Dhruv-x7x/Universal-Wireless-Programmer/others/GUI_flowchart.jpeg

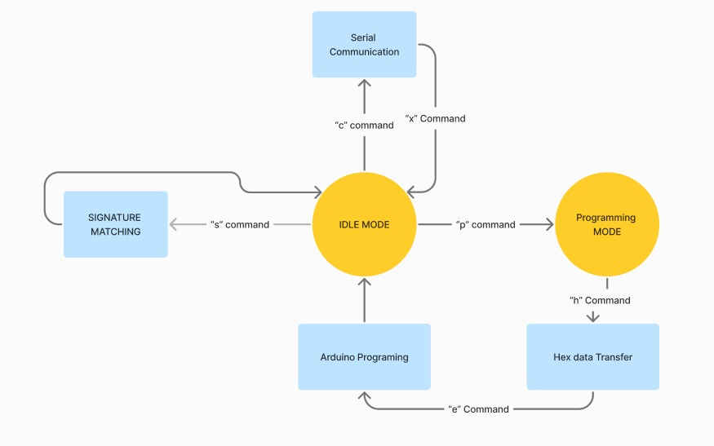
others/GUI_flowchart.jpeg
