Dhruv-x7x/Universal-Wireless-Programmer/pcb/PCB1/pictures/pcb_3d_back.jpeg

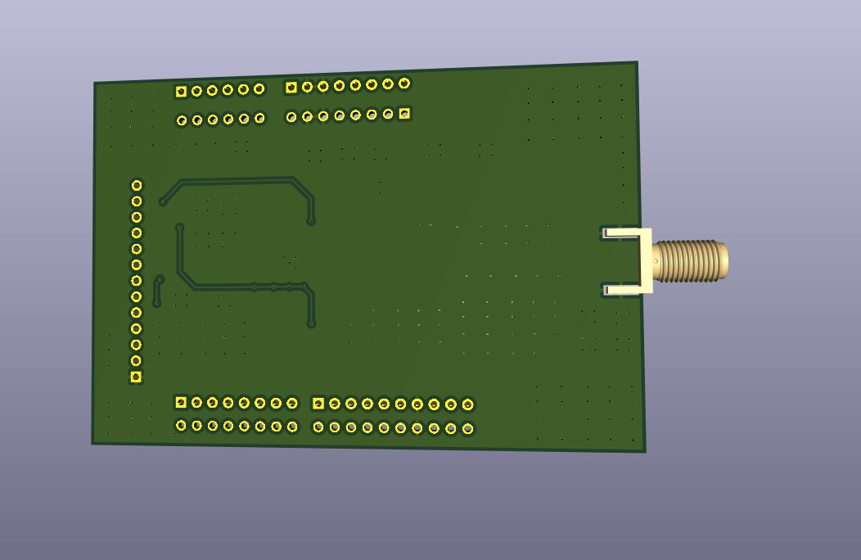
pcb/PCB1/pictures/pcb_3d_back.jpeg
