Dhruv-x7x/Universal-Wireless-Programmer/pcb/PCB1/pictures/pcb_3d_front.jpeg

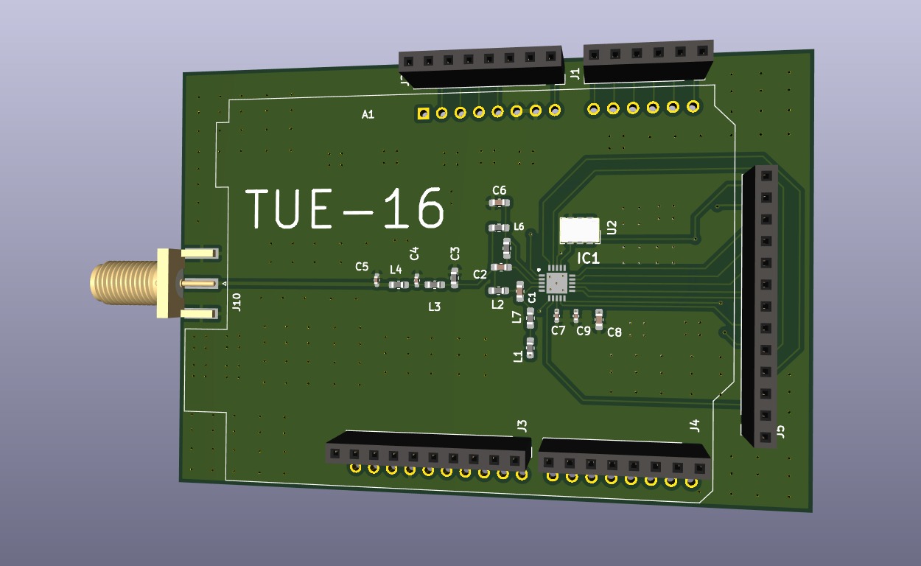
pcb/PCB1/pictures/pcb_3d_front.jpeg
