Dhruv-x7x/Universal-Wireless-Programmer/pcb/PCB1/pictures/pcb_board.jpg

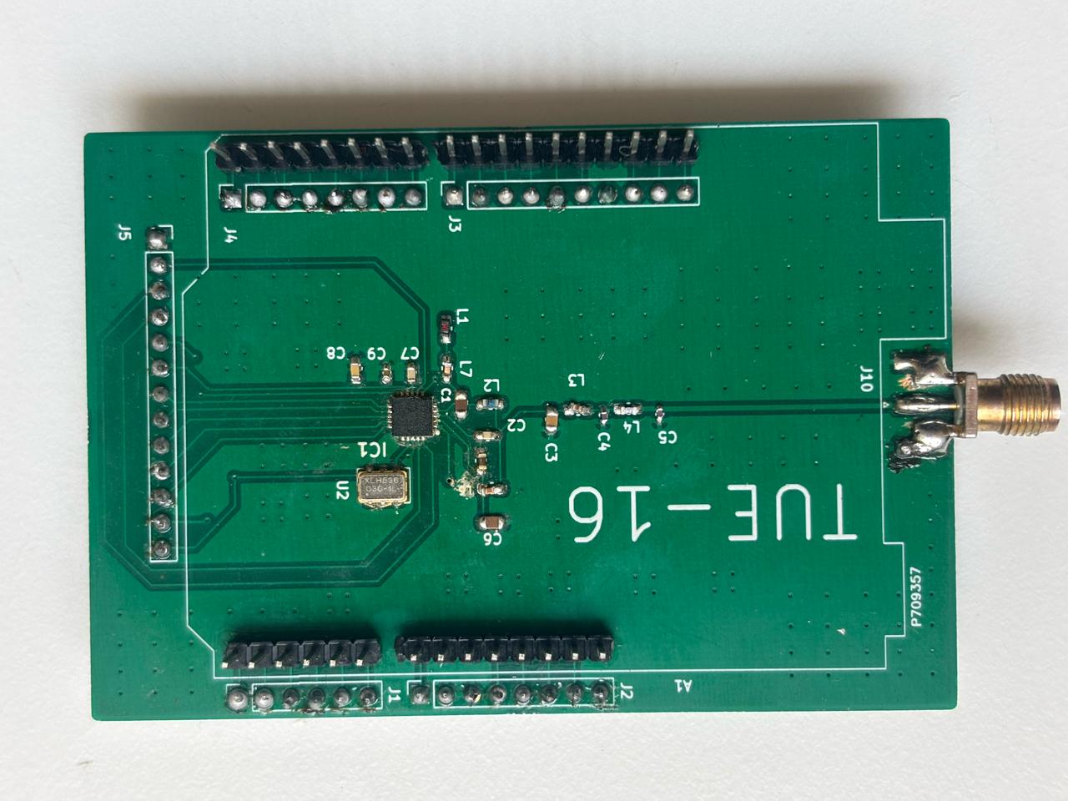
pcb/PCB1/pictures/pcb_board.jpg
