Dhruv-x7x/Universal-Wireless-Programmer/pcb/PCB1/pictures/pcb_with_antenna.jpg

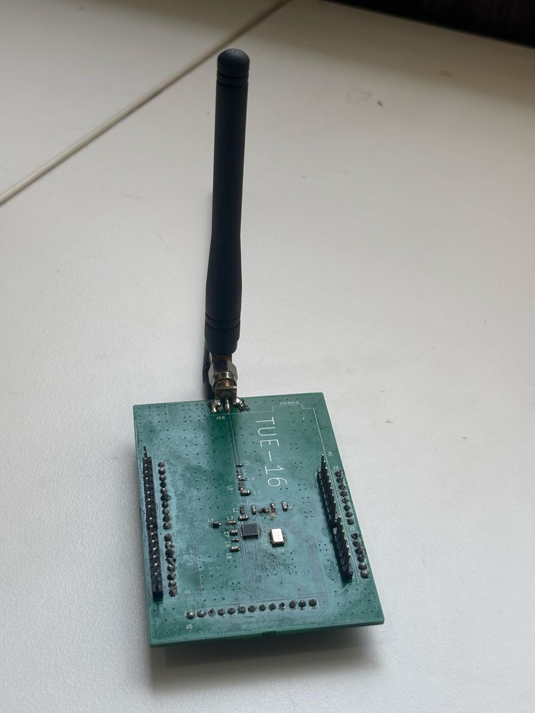
pcb/PCB1/pictures/pcb_with_antenna.jpg
