Dhruv-x7x/Universal-Wireless-Programmer/src/STM32/USB_Detect/Core/Src/main.c

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
/* Includes ------------------------------------------------------------------*/
#include "main.h"
#include "usart.h"
#include "usb_host.h"
#include "gpio.h"
#include <string.h>  /* Include for strcmp */

/* USER CODE BEGIN PD */
#define MAX_BOARD_NAME_LENGTH 50
char detected_board_name[MAX_BOARD_NAME_LENGTH] = "No Device";  // Store the detected board name
char selected_board_name[MAX_BOARD_NAME_LENGTH] = "Arduino UNO R3";  // You can set this to the selected board's name

/* USER CODE END PD */


void SystemClock_Config(void);
void MX_USB_HOST_Process(void);

/**
  * @brief  The application entry point.
  * @retval int
  */
int main(void)
{

  /* MCU Configuration--------------------------------------------------------*/

  /* Reset of all peripherals, Initializes the Flash interface and the Systick. */
  HAL_Init();

  /* Configure the system clock */
  SystemClock_Config();

  /* Initialize all configured peripherals */
  MX_GPIO_Init();
  MX_USART2_UART_Init();
  MX_USB_HOST_Init();
  /* Infinite loop */
  /* USER CODE BEGIN WHILE */
  while (1)
  {
      const char* detected_device = check_usb_device();  // Get the name of the detected device
      strncpy(detected_board_name, detected_device, MAX_BOARD_NAME_LENGTH - 1);
      detected_board_name[MAX_BOARD_NAME_LENGTH - 1] = '\0'; // Ensure null termination

      if (strcmp(detected_board_name, "No Device") == 0) {
          // If no device is detected, do nothing or handle accordingly
          printf("No USB device detected.\r\n");
      } else {
          // If a device is detected, check if it matches the selected board
          if (strcmp(detected_board_name, selected_board_name) == 0) {
              printf("Detected board matches the selected board: %s\r\n", detected_board_name);
              if (strcmp(detected_board_name, "Arduino UNO R3") == 0) {  // Corrected comparison
                      printf("Triggering bootloader\r\n");
                      trigger_arduino_bootloader();
                  }
          } else {
              printf("Board mismatch! Detected: %s, Selected: %s\r\n", detected_board_name, selected_board_name);
          }
      }

      MX_USB_HOST_Process();  // Process USB Host tasks
      HAL_Delay(250);  // Small delay to avoid too fast polling
  }

  /* USER CODE END 3 */
}

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
