Dhruv-x7x/Universal-Wireless-Programmer/src/STM32/HardcodeRXTX/Core/Inc/arduino_hex.h

/**
  * @file    arduino_hex.h
  * @brief   Arduino hex file data
  * @details Contains the hex file data to be programmed to the Arduino
  *          Generated from Blink.ino.hex
  */

#ifndef ARDUINO_HEX_H
#define ARDUINO_HEX_H
#include <stdint.h>


/* Arduino hex file data as byte array */
const uint8_t arduino_hex_data[] = {
    /* Line 1 */
    ':', '1', '0', '0', '0', '0', '0', '0', '0', '0', 'C', '9', '4', '5', 'C', '0',
    '0', '0', 'C', '9', '4', '6', 'E', '0', '0', '0', 'C', '9', '4', '6', 'E', '0',
    '0', '0', 'C', '9', '4', '6', 'E', '0', '0', 'C', 'A',
    /* Line 2 */
    ':', '1', '0', '0', '0', '1', '0', '0', '0', '0', 'C', '9', '4', '6', 'E', '0',
    '0', '0', 'C', '9', '4', '6', 'E', '0', '0', '0', 'C', '9', '4', '6', 'E', '0',
    '0', '0', 'C', '9', '4', '6', 'E', '0', '0', 'A', '8',
    /* Line 3 */
    ':', '1', '0', '0', '0', '2', '0', '0', '0', '0', 'C', '9', '4', '6', 'E', '0',
    '0', '0', 'C', '9', '4', '6', 'E', '0', '0', '0', 'C', '9', '4', '6', 'E', '0',
    '0', '0', 'C', '9', '4', '6', 'E', '0', '0', '9', '8',
    /* Line 4 */
    ':', '1', '0', '0', '0', '3', '0', '0', '0', '0', 'C', '9', '4', '6', 'E', '0',
    '0', '0', 'C', '9', '4', '6', 'E', '0', '0', '0', 'C', '9', '4', '6', 'E', '0',
    '0', '0', 'C', '9', '4', '6', 'E', '0', '0', '8', '8',
    /* Line 5 */
    ':', '1', '0', '0', '0', '4', '0', '0', '0', '0', 'C', '9', '4', '1', '3', '0',
    '1', '0', 'C', '9', '4', '6', 'E', '0', '0', '0', 'C', '9', '4', '6', 'E', '0',
    '0', '0', 'C', '9', '4', '6', 'E', '0', '0', 'D', '2',
    /* Line 6 */
    ':', '1', '0', '0', '0', '5', '0', '0', '0', '0', 'C', '9', '4', '6', 'E', '0',
    '0', '0', 'C', '9', '4', '6', 'E', '0', '0', '0', 'C', '9', '4', '6', 'E', '0',
    '0', '0', 'C', '9', '4', '6', 'E', '0', '0', '6', '8',
    /* Line 7 */
    ':', '1', '0', '0', '0', '6', '0', '0', '0', '0', 'C', '9', '4', '6', 'E', '0',
    '0', '0', 'C', '9', '4', '6', 'E', '0', '0', '0', '0', '0', '0', '0', '0', '0',
    '0', '2', '4', '0', '0', '2', '7', '0', '0', '2', '9',
    /* Line 8 */
    ':', '1', '0', '0', '0', '7', '0', '0', '0', '2', 'A', '0', '0', '0', '0', '0',
    '0', '0', '0', '0', '0', '2', '5', '0', '0', '2', '8', '0', '0', '2', 'B', '0',
    '0', '0', '4', '0', '4', '0', '4', '0', '4', 'C', 'E',
    /* Line 9 */
    ':', '1', '0', '0', '0', '8', '0', '0', '0', '0', '4', '0', '4', '0', '4', '0',
    '4', '0', '2', '0', '2', '0', '2', '0', '2', '0', '2', '0', '2', '0', '3', '0',
    '3', '0', '3', '0', '3', '0', '3', '0', '3', '4', '2',
    /* Line 10 */
    ':', '1', '0', '0', '0', '9', '0', '0', '0', '0', '1', '0', '2', '0', '4', '0',
    '8', '1', '0', '2', '0', '4', '0', '8', '0', '0', '1', '0', '2', '0', '4', '0',
    '8', '1', '0', '2', '0', '0', '1', '0', '2', '1', 'F',
    /* Line 11 */
    ':', '1', '0', '0', '0', 'A', '0', '0', '0', '0', '4', '0', '8', '1', '0', '2',
    '0', '0', '0', '0', '0', '0', '0', '0', '8', '0', '0', '0', '2', '0', '1', '0',
    '0', '0', '0', '0', '3', '0', '4', '0', '7', 'F', 'B',
    /* Line 12 */
    ':', '1', '0', '0', '0', 'B', '0', '0', '0', '0', '0', '0', '0', '0', '0', '0',
    '0', '0', '0', '0', '0', '0', '0', '0', '0', '1', '1', '2', '4', '1', 'F', 'B',
    'E', 'C', 'F', 'E', 'F', 'D', '8', 'E', '0', 'B', '8',
    /* Line 13 */
    ':', '1', '0', '0', '0', 'C', '0', '0', '0', 'D', 'E', 'B', 'F', 'C', 'D', 'B',
    'F', '2', '1', 'E', '0', 'A', '0', 'E', '0', 'B', '1', 'E', '0', '0', '1', 'C',
    '0', '1', 'D', '9', '2', 'A', '9', '3', '0', 'A', 'C',
    /* Line 14 */
    ':', '1', '0', '0', '0', 'D', '0', '0', '0', 'B', '2', '0', '7', 'E', '1', 'F',
    '7', '0', 'E', '9', '4', '5', 'D', '0', '1', '0', 'C', '9', '4', 'C', 'C', '0',
    '1', '0', 'C', '9', '4', '0', '0', '0', '0', '8', '2',
    /* Line 15 */
    ':', '1', '0', '0', '0', 'E', '0', '0', '0', 'E', '1', 'E', 'B', 'F', '0', 'E',
    '0', '2', '4', '9', '1', 'E', 'D', 'E', '9', 'F', '0', 'E', '0', '9', '4', '9',
    '1', 'E', '9', 'E', '8', 'F', '0', 'E', '0', '5', '3',
    /* Line 16 */
    ':', '1', '0', '0', '0', 'F', '0', '0', '0', 'E', '4', '9', '1', 'E', 'E', '2',
    '3', 'C', '9', 'F', '0', '2', '2', '2', '3', '3', '9', 'F', '0', '2', '3', '3',
    '0', '0', '1', 'F', '1', 'A', '8', 'F', '4', '7', '2',
    /* Line 17 */
    ':', '1', '0', '0', '1', '0', '0', '0', '0', '2', '1', '3', '0', '1', '9', 'F',
    '1', '2', '2', '3', '0', '2', '9', 'F', '1', 'F', '0', 'E', '0', 'E', 'E', '0',
    'F', 'F', 'F', '1', 'F', 'E', 'E', '5', '8', 'F', '7',
    /* Line 18 */
    ':', '1', '0', '0', '1', '1', '0', '0', '0', 'F', 'F', '4', 'F', 'A', '5', '9',
    '1', 'B', '4', '9', '1', '2', 'F', 'B', '7', 'F', '8', '9', '4', 'E', 'C', '9',
    '1', '8', '1', '1', '1', '2', '6', 'C', '0', 'A', 'F',
    /* Line 19 */
    ':', '1', '0', '0', '1', '2', '0', '0', '0', '9', '0', '9', '5', '9', 'E', '2',
    '3', '9', 'C', '9', '3', '2', 'F', 'B', 'F', '0', '8', '9', '5', '2', '7', '3',
    '0', 'A', '9', 'F', '0', '2', '8', '3', '0', 'E', '7',
    /* Line 20 */
    ':', '1', '0', '0', '1', '3', '0', '0', '0', 'C', '9', 'F', '0', '2', '4', '3',
    '0', '4', '9', 'F', '7', '2', '0', '9', '1', '8', '0', '0', '0', '2', 'F', '7',
    'D', '0', '3', 'C', '0', '2', '0', '9', '1', '2', '1',
    /* Line 21 */
    ':', '1', '0', '0', '1', '4', '0', '0', '0', '8', '0', '0', '0', '2', 'F', '7',
    '7', '2', '0', '9', '3', '8', '0', '0', '0', 'D', 'F', 'C', 'F', '2', '4', 'B',
    '5', '2', 'F', '7', '7', '2', '4', 'B', 'D', '4', '8',
    /* Line 22 */
    ':', '1', '0', '0', '1', '5', '0', '0', '0', 'D', 'B', 'C', 'F', '2', '4', 'B',
    '5', '2', 'F', '7', 'D', 'F', 'B', 'C', 'F', '2', '0', '9', '1', 'B', '0', '0',
    '0', '2', 'F', '7', '7', '2', '0', '9', '3', 'E', 'C',
    /* Line 23 */
    ':', '1', '0', '0', '1', '6', '0', '0', '0', 'B', '0', '0', '0', 'D', '2', 'C',
    'F', '2', '0', '9', '1', 'B', '0', '0', '0', '2', 'F', '7', 'D', 'F', '9', 'C',
    'F', '9', 'E', '2', 'B', 'D', 'A', 'C', 'F', 'F', '7',
    /* Line 24 */
    ':', '1', '0', '0', '1', '7', '0', '0', '0', '3', 'F', 'B', '7', 'F', '8', '9',
    '4', '8', '0', '9', '1', '0', '5', '0', '1', '9', '0', '9', '1', '0', '6', '0',
    '1', 'A', '0', '9', '1', '0', '7', '0', '1', '8', '5',
    /* Line 25 */
    ':', '1', '0', '0', '1', '8', '0', '0', '0', 'B', '0', '9', '1', '0', '8', '0',
    '1', '2', '6', 'B', '5', 'A', '8', '9', 'B', '0', '5', 'C', '0', '2', 'F', '3',
    'F', '1', '9', 'F', '0', '0', '1', '9', '6', '3', '4',
    /* Line 26 */
    ':', '1', '0', '0', '1', '9', '0', '0', '0', 'A', '1', '1', 'D', 'B', '1', '1',
    'D', '3', 'F', 'B', 'F', 'B', 'A', '2', 'F', 'A', '9', '2', 'F', '9', '8', '2',
    'F', '8', '8', '2', '7', 'B', 'C', '0', '1', 'E', '1',
    /* Line 27 */
    ':', '1', '0', '0', '1', 'A', '0', '0', '0', 'C', 'D', '0', '1', '6', '2', '0',
    'F', '7', '1', '1', 'D', '8', '1', '1', 'D', '9', '1', '1', 'D', '4', '2', 'E',
    '0', '6', '6', '0', 'F', '7', '7', '1', 'F', '0', '9',
    /* Line 28 */
    ':', '1', '0', '0', '1', 'B', '0', '0', '0', '8', '8', '1', 'F', '9', '9', '1',
    'F', '4', 'A', '9', '5', 'D', '1', 'F', '7', '0', '8', '9', '5', '8', 'F', '9',
    '2', '9', 'F', '9', '2', 'A', 'F', '9', '2', '0', '9',
    /* Line 29 */
    ':', '1', '0', '0', '1', 'C', '0', '0', '0', 'B', 'F', '9', '2', 'C', 'F', '9',
    '2', 'D', 'F', '9', '2', 'E', 'F', '9', '2', 'F', 'F', '9', '2', '0', 'E', '9',
    '4', 'B', '8', '0', '0', '4', 'B', '0', '1', '5', '4',
    /* Line 30 */
    ':', '1', '0', '0', '1', 'D', '0', '0', '0', '5', 'C', '0', '1', '8', '8', 'E',
    'E', 'C', '8', '2', 'E', '8', '3', 'E', '0', 'D', '8', '2', 'E', 'E', '1', '2',
    'C', 'F', '1', '2', 'C', '0', 'E', '9', '4', '2', '1',
    /* Line 31 */
    ':', '1', '0', '0', '1', 'E', '0', '0', '0', 'B', '8', '0', '0', '6', '8', '1',
    '9', '7', '9', '0', '9', '8', 'A', '0', '9', '9', 'B', '0', '9', '6', '8', '3',
    'E', '7', '3', '4', '0', '8', '1', '0', '5', '3', 'E',
    /* Line 32 */
    ':', '1', '0', '0', '1', 'F', '0', '0', '0', '9', '1', '0', '5', 'A', '8', 'F',
    '3', '2', '1', 'E', '0', 'C', '2', '1', 'A', 'D', '1', '0', '8', 'E', '1', '0',
    '8', 'F', '1', '0', '8', '8', '8', 'E', 'E', 'C', '0',
    /* Line 33 */
    ':', '1', '0', '0', '2', '0', '0', '0', '0', '8', '8', '0', 'E', '8', '3', 'E',
    '0', '9', '8', '1', 'E', 'A', '1', '1', 'C', 'B', '1', '1', 'C', 'C', '1', '1',
    '4', 'D', '1', '0', '4', 'E', '1', '0', '4', '2', '6',
    /* Line 34 */
    ':', '1', '0', '0', '2', '1', '0', '0', '0', 'F', '1', '0', '4', '2', '9', 'F',
    '7', 'F', 'F', '9', '0', 'E', 'F', '9', '0', 'D', 'F', '9', '0', 'C', 'F', '9',
    '0', 'B', 'F', '9', '0', 'A', 'F', '9', '0', '5', 'F',
    /* Line 35 */
    ':', '1', '0', '0', '2', '2', '0', '0', '0', '9', 'F', '9', '0', '8', 'F', '9',
    '0', '0', '8', '9', '5', '1', 'F', '9', '2', '0', 'F', '9', '2', '0', 'F', 'B',
    '6', '0', 'F', '9', '2', '1', '1', '2', '4', 'F', '6',
    /* Line 36 */
    ':', '1', '0', '0', '2', '3', '0', '0', '0', '2', 'F', '9', '3', '3', 'F', '9',
    '3', '8', 'F', '9', '3', '9', 'F', '9', '3', 'A', 'F', '9', '3', 'B', 'F', '9',
    '3', '8', '0', '9', '1', '0', '1', '0', '1', '2', 'F',
    /* Line 37 */
    ':', '1', '0', '0', '2', '4', '0', '0', '0', '9', '0', '9', '1', '0', '2', '0',
    '1', 'A', '0', '9', '1', '0', '3', '0', '1', 'B', '0', '9', '1', '0', '4', '0',
    '1', '3', '0', '9', '1', '0', '0', '0', '1', '4', 'D',
    /* Line 38 */
    ':', '1', '0', '0', '2', '5', '0', '0', '0', '2', '3', 'E', '0', '2', '3', '0',
    'F', '2', 'D', '3', '7', '5', '8', 'F', '5', '0', '1', '9', '6', 'A', '1', '1',
    'D', 'B', '1', '1', 'D', '2', '0', '9', '3', 'E', '2',
    /* Line 39 */
    ':', '1', '0', '0', '2', '6', '0', '0', '0', '0', '0', '0', '1', '8', '0', '9',
    '3', '0', '1', '0', '1', '9', '0', '9', '3', '0', '2', '0', '1', 'A', '0', '9',
    '3', '0', '3', '0', '1', 'B', '0', '9', '3', 'D', '8',
    /* Line 40 */
    ':', '1', '0', '0', '2', '7', '0', '0', '0', '0', '4', '0', '1', '8', '0', '9',
    '1', '0', '5', '0', '1', '9', '0', '9', '1', '0', '6', '0', '1', 'A', '0', '9',
    '1', '0', '7', '0', '1', 'B', '0', '9', '1', 'C', '0',
    /* Line 41 */
    ':', '1', '0', '0', '2', '8', '0', '0', '0', '0', '8', '0', '1', '0', '1', '9',
    '6', 'A', '1', '1', 'D', 'B', '1', '1', 'D', '8', '0', '9', '3', '0', '5', '0',
    '1', '9', '0', '9', '3', '0', '6', '0', '1', 'F', 'F',
    /* Line 42 */
    ':', '1', '0', '0', '2', '9', '0', '0', '0', 'A', '0', '9', '3', '0', '7', '0',
    '1', 'B', '0', '9', '3', '0', '8', '0', '1', 'B', 'F', '9', '1', 'A', 'F', '9',
    '1', '9', 'F', '9', '1', '8', 'F', '9', '1', 'F', '7',
    /* Line 43 */
    ':', '1', '0', '0', '2', 'A', '0', '0', '0', '3', 'F', '9', '1', '2', 'F', '9',
    '1', '0', 'F', '9', '0', '0', 'F', 'B', 'E', '0', 'F', '9', '0', '1', 'F', '9',
    '0', '1', '8', '9', '5', '2', '6', 'E', '8', '4', '9',
    /* Line 44 */
    ':', '1', '0', '0', '2', 'B', '0', '0', '0', '2', '3', '0', 'F', '0', '2', '9',
    '6', 'A', '1', '1', 'D', 'B', '1', '1', 'D', 'D', '2', 'C', 'F', '7', '8', '9',
    '4', '8', '4', 'B', '5', '8', '2', '6', '0', '2', '0',
    /* Line 45 */
    ':', '1', '0', '0', '2', 'C', '0', '0', '0', '8', '4', 'B', 'D', '8', '4', 'B',
    '5', '8', '1', '6', '0', '8', '4', 'B', 'D', '8', '5', 'B', '5', '8', '2', '6',
    '0', '8', '5', 'B', 'D', '8', '5', 'B', '5', 'F', 'A',
    /* Line 46 */
    ':', '1', '0', '0', '2', 'D', '0', '0', '0', '8', '1', '6', '0', '8', '5', 'B',
    'D', '8', '0', '9', '1', '6', 'E', '0', '0', '8', '1', '6', '0', '8', '0', '9',
    '3', '6', 'E', '0', '0', '1', '0', '9', '2', '7', '8',
    /* Line 47 */
    ':', '1', '0', '0', '2', 'E', '0', '0', '0', '8', '1', '0', '0', '8', '0', '9',
    '1', '8', '1', '0', '0', '8', '2', '6', '0', '8', '0', '9', '3', '8', '1', '0',
    '0', '8', '0', '9', '1', '8', '1', '0', '0', 'F', '3',
    /* Line 48 */
    ':', '1', '0', '0', '2', 'F', '0', '0', '0', '8', '1', '6', '0', '8', '0', '9',
    '3', '8', '1', '0', '0', '8', '0', '9', '1', '8', '0', '0', '0', '8', '1', '6',
    '0', '8', '0', '9', '3', '8', '0', '0', '0', '8', '4',
    /* Line 49 */
    ':', '1', '0', '0', '3', '0', '0', '0', '0', '8', '0', '9', '1', 'B', '1', '0',
    '0', '8', '4', '6', '0', '8', '0', '9', '3', 'B', '1', '0', '0', '8', '0', '9',
    '1', 'B', '0', '0', '0', '8', '1', '6', '0', 'E', '1',
    /* Line 50 */
    ':', '1', '0', '0', '3', '1', '0', '0', '0', '8', '0', '9', '3', 'B', '0', '0',
    '0', '8', '0', '9', '1', '7', 'A', '0', '0', '8', '4', '6', '0', '8', '0', '9',
    '3', '7', 'A', '0', '0', '8', '0', '9', '1', '0', 'D',
    /* Line 51 */
    ':', '1', '0', '0', '3', '2', '0', '0', '0', '7', 'A', '0', '0', '8', '2', '6',
    '0', '8', '0', '9', '3', '7', 'A', '0', '0', '8', '0', '9', '1', '7', 'A', '0',
    '0', '8', '1', '6', '0', '8', '0', '9', '3', '6', '5',
    /* Line 52 */
    ':', '1', '0', '0', '3', '3', '0', '0', '0', '7', 'A', '0', '0', '8', '0', '9',
    '1', '7', 'A', '0', '0', '8', '0', '6', '8', '8', '0', '9', '3', '7', 'A', '0',
    '0', '1', '0', '9', '2', 'C', '1', '0', '0', 'E', '0',
    /* Line 53 */
    ':', '1', '0', '0', '3', '4', '0', '0', '0', 'E', 'D', 'E', '9', 'F', '0', 'E',
    '0', '2', '4', '9', '1', 'E', '9', 'E', '8', 'F', '0', 'E', '0', '8', '4', '9',
    '1', '8', '8', '2', '3', '9', '9', 'F', '0', '6', '8',
    /* Line 54 */
    ':', '1', '0', '0', '3', '5', '0', '0', '0', '9', '0', 'E', '0', '8', '8', '0',
    'F', '9', '9', '1', 'F', 'F', 'C', '0', '1', 'E', '8', '5', '9', 'F', 'F', '4',
    'F', 'A', '5', '9', '1', 'B', '4', '9', '1', 'D', '7',
    /* Line 55 */
    ':', '1', '0', '0', '3', '6', '0', '0', '0', 'F', 'C', '0', '1', 'E', 'E', '5',
    '8', 'F', 'F', '4', 'F', '8', '5', '9', '1', '9', '4', '9', '1', '8', 'F', 'B',
    '7', 'F', '8', '9', '4', 'E', 'C', '9', '1', '7', '2',
    /* Line 56 */
    ':', '1', '0', '0', '3', '7', '0', '0', '0', 'E', '2', '2', 'B', 'E', 'C', '9',
    '3', '8', 'F', 'B', 'F', 'C', '0', 'E', '0', 'D', '0', 'E', '0', '8', '1', 'E',
    '0', '0', 'E', '9', '4', '7', '0', '0', '0', 'E', '0',
    /* Line 57 */
    ':', '1', '0', '0', '3', '8', '0', '0', '0', '0', 'E', '9', '4', 'D', 'D', '0',
    '0', '8', '0', 'E', '0', '0', 'E', '9', '4', '7', '0', '0', '0', '0', 'E', '9',
    '4', 'D', 'D', '0', '0', '2', '0', '9', '7', '4', '6',
    /* Line 58 */
    ':', '0', 'C', '0', '3', '9', '0', '0', '0', 'A', '1', 'F', '3', '0', 'E', '9',
    '4', '0', '0', '0', '0', 'F', '1', 'C', 'F', 'F', '8', '9', '4', 'F', 'F', 'C',
    'F', '1', '1',
    /* Line 59 */
    ':', '0', '0', '0', '0', '0', '0', '0', '1', 'F', 'F'
};

const uint32_t arduino_hex_size = sizeof(arduino_hex_data);

#endif /* ARDUINO_HEX_H */
